Aassimrepo/4S-BMS-Proteus-KiCad/KiCad_PCB/Outputs/PCB RENDER.png

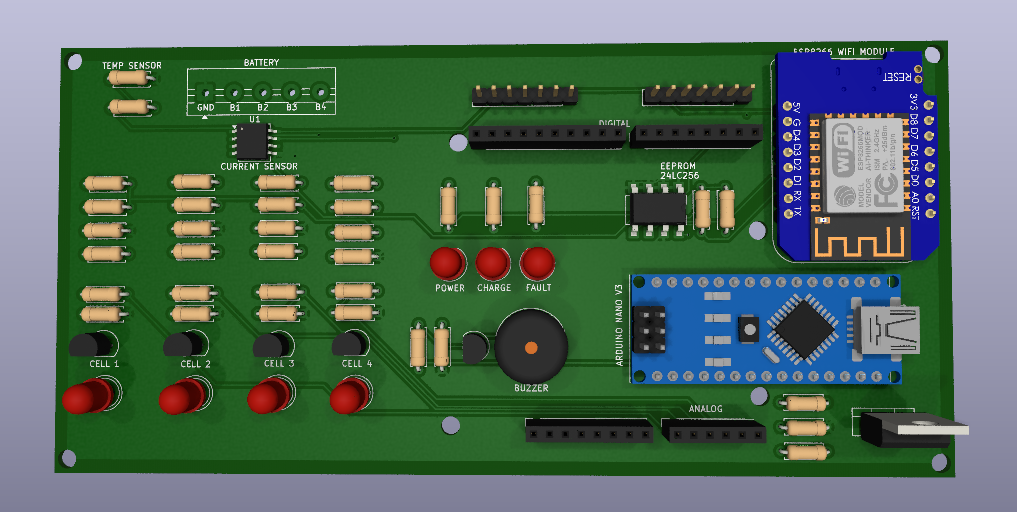
KiCad_PCB/Outputs/PCB RENDER.png
