Aassimrepo/4S-BMS-Proteus-KiCad/KiCad_PCB/Outputs/PCB PLACEMENT.png

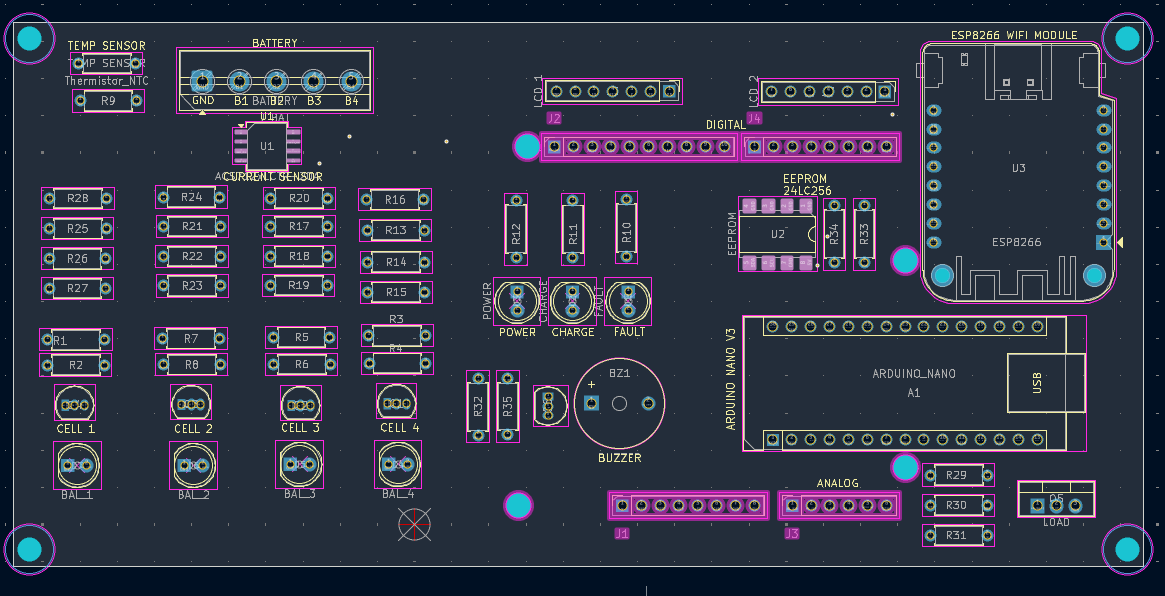
KiCad_PCB/Outputs/PCB PLACEMENT.png
