Aassimrepo/4S-BMS-Proteus-KiCad/KiCad_PCB/Outputs/PCB WIRING.png

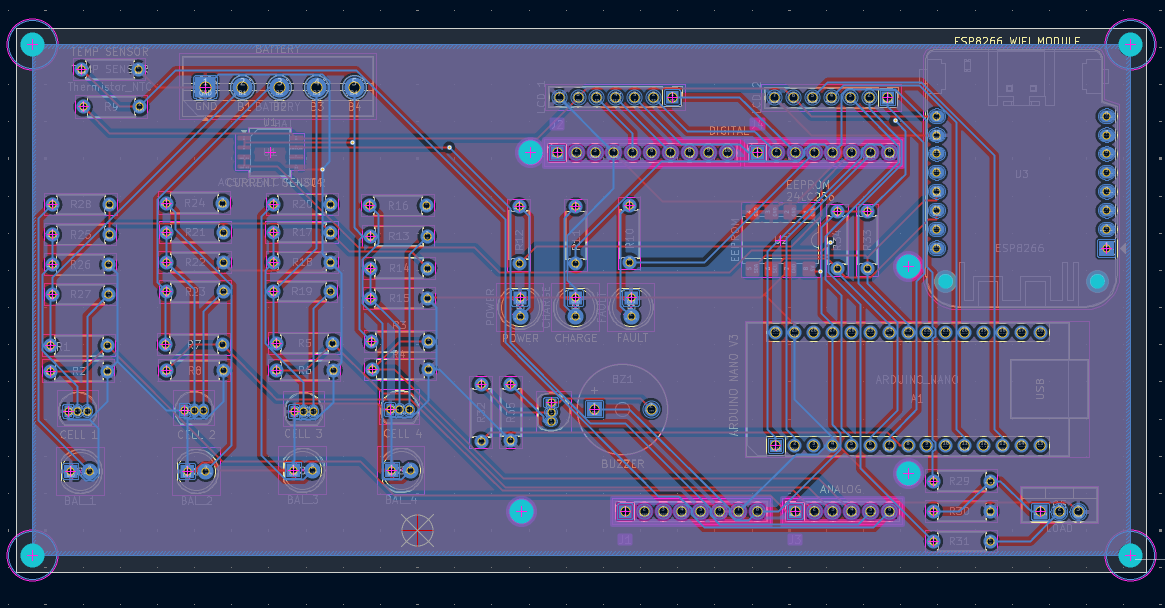
KiCad_PCB/Outputs/PCB WIRING.png
